minhquyminhquy/MediCopter-Drone/codes/function-test-scripts/TestSpinningMotors.py

#from os import wait_result
from dronekit import connect, VehicleMode, LocationGlobalRelative, APIException
import time
import socket
import exception
import math
import argparse

def connectMyCopter():
    parser = argparse.ArgumentParser(description='commands')
    parser.add_argument("--connect")
    args = parser.parse_args()

    connection_string = args.connect
    baud_rate = 57600

    vehicle = connect(connection_string, baud = baud_rate, wait_ready=True)

    return vehicle

def arm():
    while vehicle.is_armable==False:
        print("Waiting for vehicle to become armable...")
        time.sleep(1)

    print("Is armable")
    print("")

    vehicle.armed=True
    while vehicle.armed==False:
        print("Waiting for drone to become armed..")
        time.sleep(1)

    print("ARMED")
    print("ARM SPINNING")

    return None

vehicle= connectMyCopter()
vehicle.mode = VehicleMode("GUIDED")
vehicle.armed = True
arm()
print("end")
